bitaxeorg/bitaxeBonanza/3d/BZM2.step

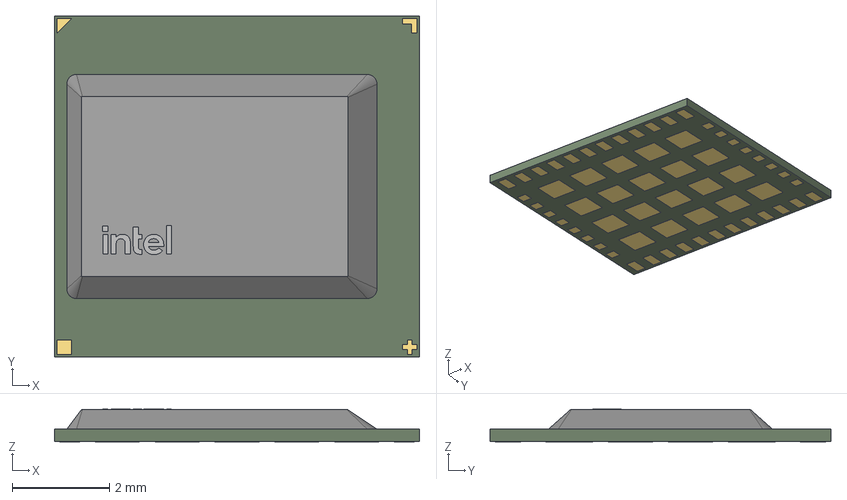
[picture p16: CAD file, 2026-02-11]
3d/BZM2.step
7.50 x 7.00 x 0.669 mm
substrate_part
die_part
underfill_part
intelLogo_part
pin1_part
square_part
plus_part
bracket_part
pads_part
