bitaxeorg/bitaxeBonanza/3d/IND_-1R5MC_SUM.step

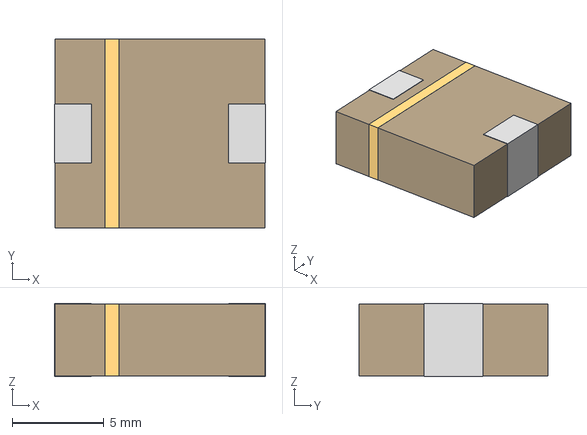
[picture p17: CAD file, 2026-02-11]
3d/IND_-1R5MC_SUM.step
11.5 x 10.3 x 3.99 mm
