bitaxeorg/bitaxeBonanza/3d/Coilcraft-XAL1060.STEP

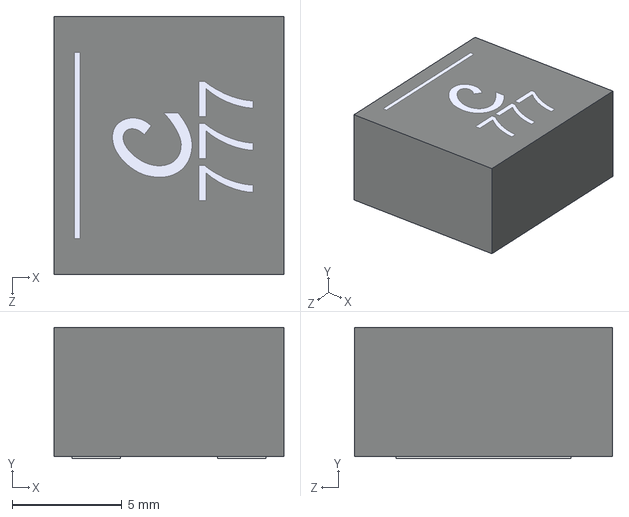
[picture p18: CAD file, 2026-02-11]
3d/Coilcraft-XAL1060.STEP
10.5 x 6.00 x 11.8 mm
