bitaxeorg/bitaxeBonanza/3d/TSM-104-01-L-SH-A.stp

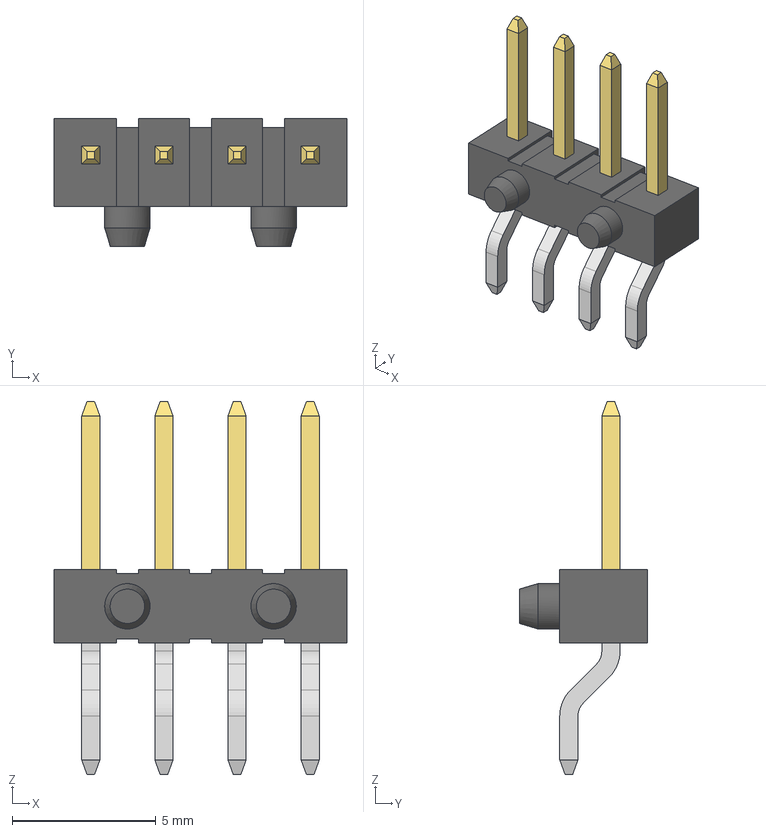
[picture p19: CAD file, 2026-02-11]
3d/TSM-104-01-L-SH-A.stp
10.2 x 4.44 x 13.0 mm
TSM-104-01-SH-A_body
T-1S6-08-L(-01-4-SH)
T-1S6-08-L(-01-4-SH)2
