bitaxeorg/bitaxeBonanza/3d/DCK0006A.stp

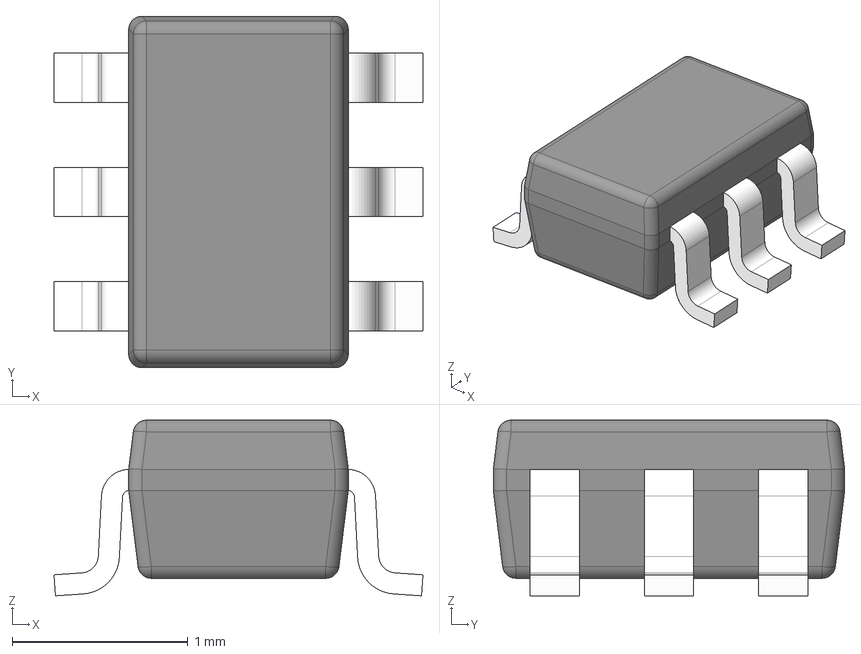
[picture p20: CAD file, 2026-02-11]
3d/DCK0006A.stp
2.10 x 2.00 x 1.00 mm
BODY-SOT
LEAD-SOT x 6
PIN1-ID
