bitaxeorg/bitaxeBonanza/3d/Fan 60x60x25mm.stp

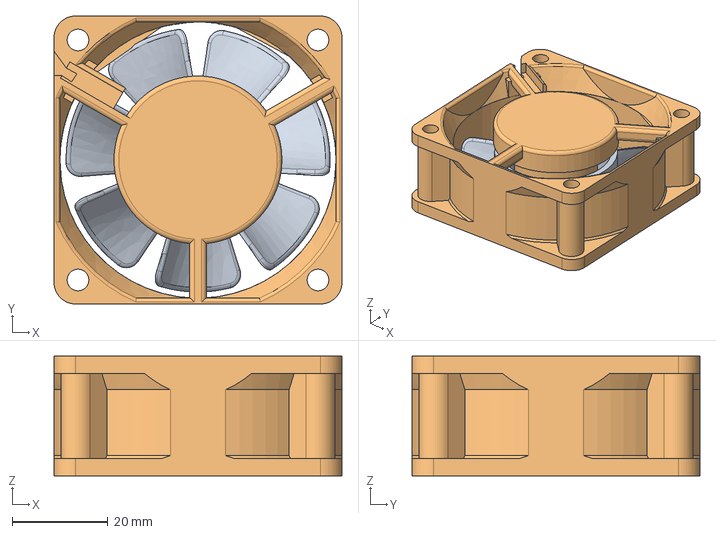
[picture p21: CAD file, 2026-02-11]
3d/Fan 60x60x25mm.stp
60.0 x 60.0 x 25.0 mm
