bitaxeorg/bitaxeBonanza/3d/RaspberryPi_Pico_W.step

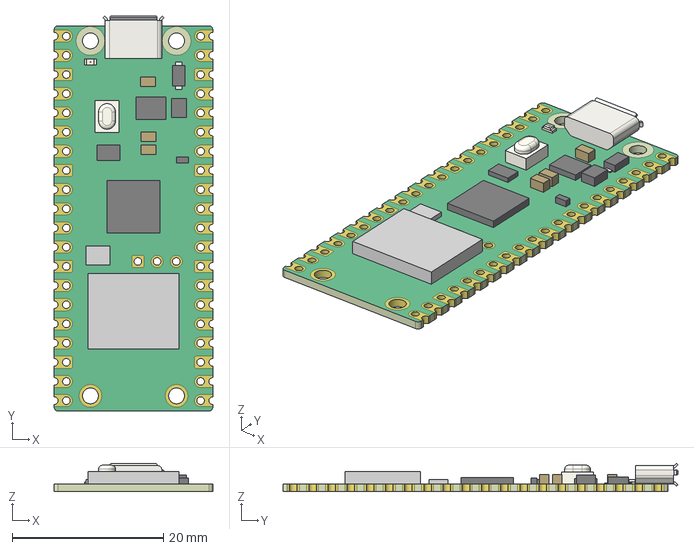
[picture p22: CAD file, 2026-02-11]
3d/RaspberryPi_Pico_W.step
21.0 x 52.3 x 3.75 mm
