bitaxeorg/bitaxeBonanza/3d/GT heatsink.step

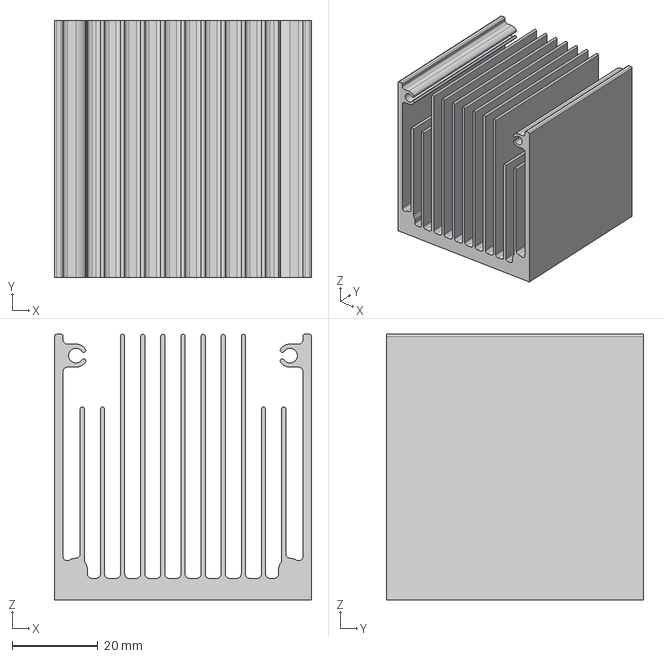
[picture p23: CAD file, 2025-06-24]
3d/GT heatsink.step
60.0 x 60.0 x 62.0 mm
