bitaxeorg/bitaxeBonanza/3d/FPC-SMD_P0.50-8P_FGS-XJ-H2.0.step

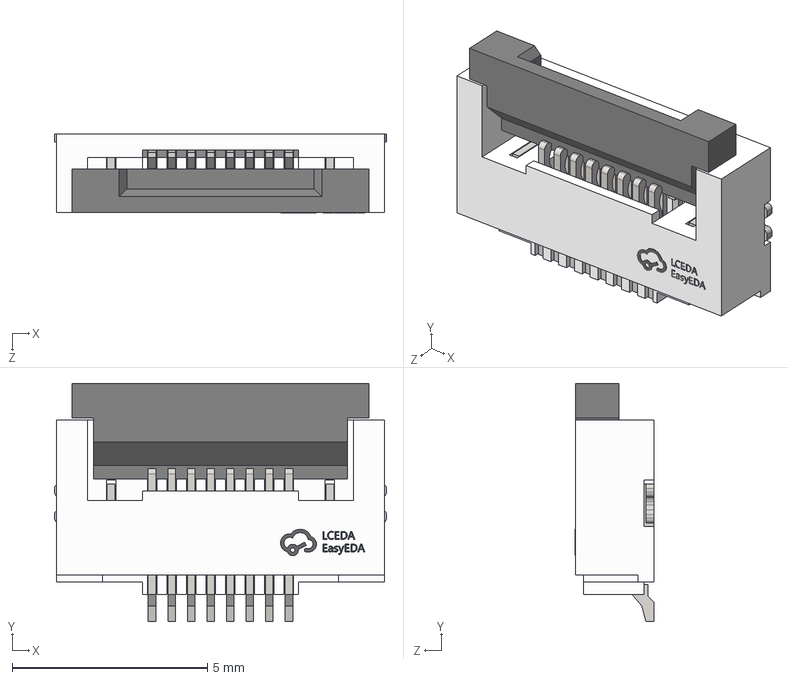
[picture p24: CAD file, 2025-06-20]
3d/FPC-SMD_P0.50-8P_FGS-XJ-H2.0.step
8.50 x 6.10 x 2.01 mm
