bitaxeorg/bitaxeBonanza/3d/FFC2B35-08-T.STEP

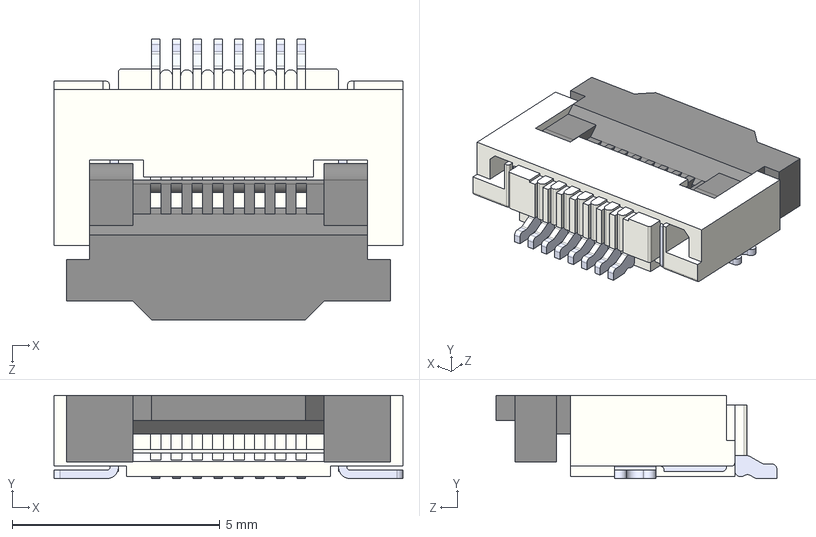
[picture p25: CAD file, 2025-06-20]
3d/FFC2B35-08-T.STEP
8.40 x 2.00 x 6.76 mm
