bitaxeorg/bitaxeBonanza/3d/BZM2model.step

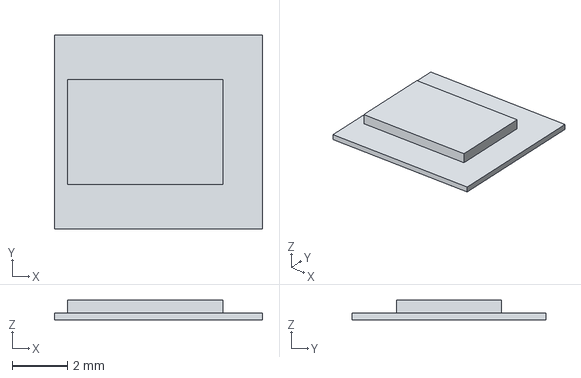
[picture p27: CAD file, 2025-06-20]
3d/BZM2model.step
7.50 x 7.00 x 0.71 mm
