bitaxeorg/bitaxeBonanza/3d/SOD-323FL_UMD2__ROM.step

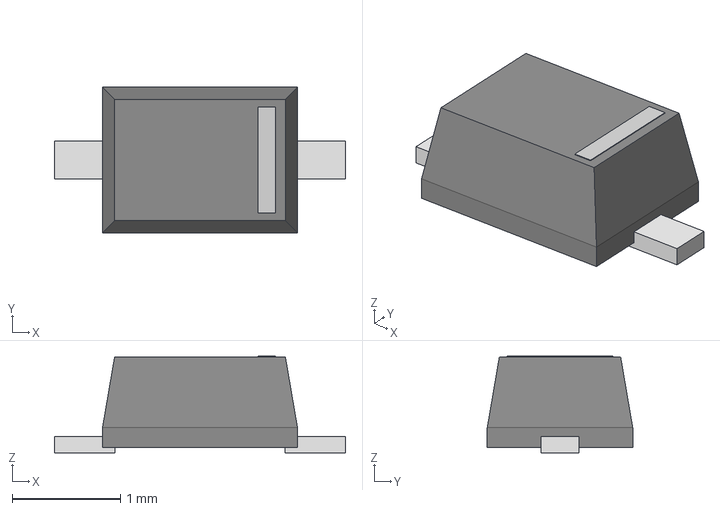
[picture p28: CAD file, 2025-06-12]
3d/SOD-323FL_UMD2__ROM.step
2.69 x 1.35 x 0.895 mm
