bitaxeorg/bitaxeBonanza/3d/DISST7789-176x320.STEP

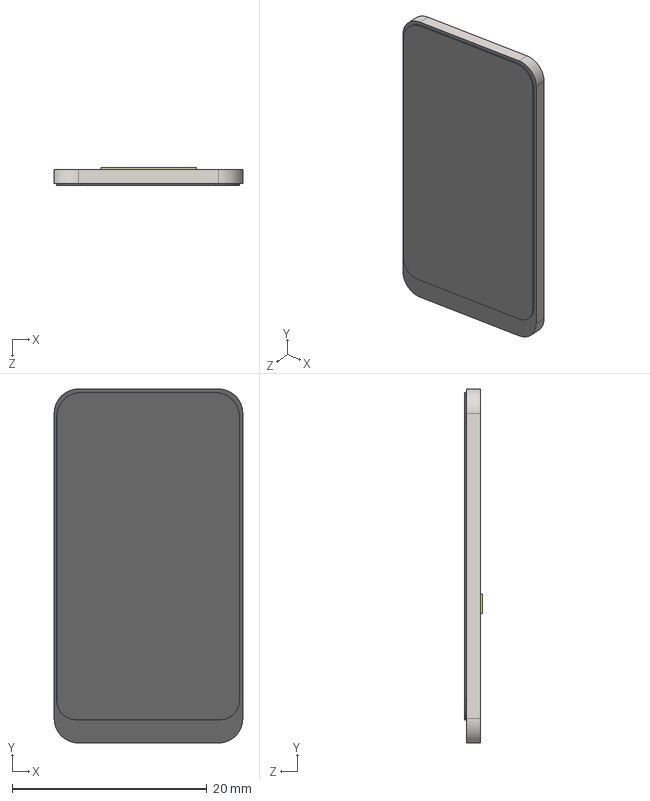
[picture p29: CAD file, 2025-03-25]
3d/DISST7789-176x320.STEP
19.4 x 36.4 x 1.86 mm
