bitaxeorg/bitaxeBonanza/3d/TXB0104RGYR.STEP

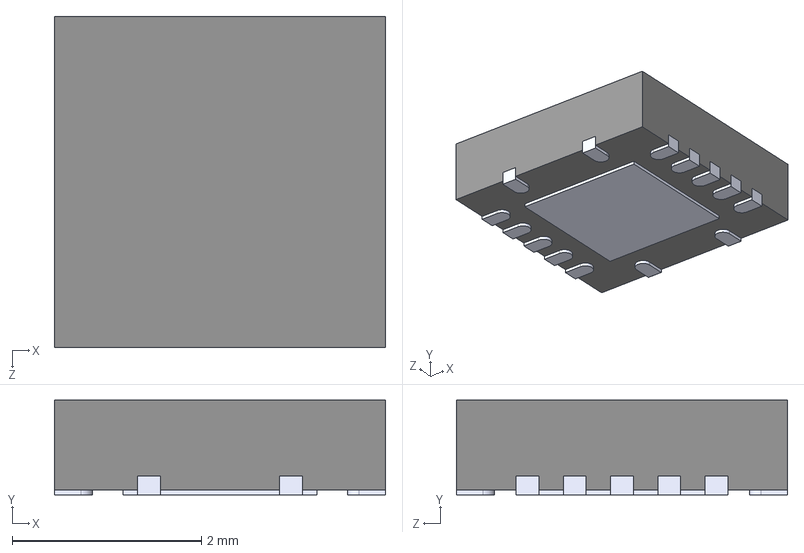
[picture p30: CAD file, 2025-03-25]
3d/TXB0104RGYR.STEP
3.50 x 1.00 x 3.50 mm
