bitaxeorg/bitaxeBonanza/3d/ESP32-S3-WROOM-1-N8R2--3DModel-STEP-56544.STEP

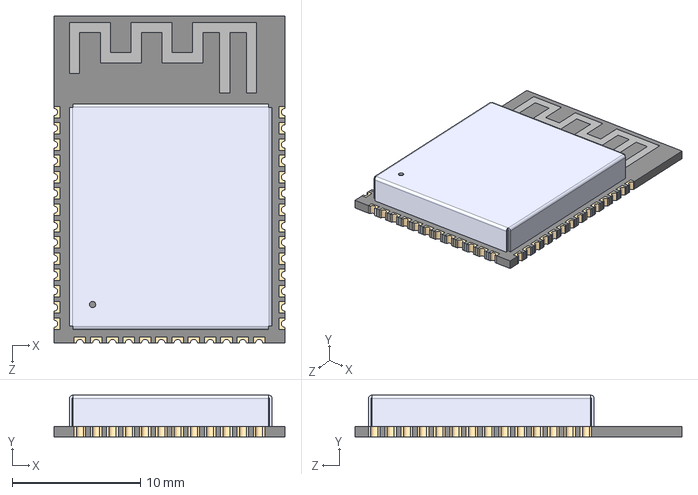
[picture p31: CAD file, 2025-03-25]
3d/ESP32-S3-WROOM-1-N8R2--3DModel-STEP-56544.STEP
18.0 x 3.25 x 25.5 mm
