bitaxeorg/bitaxeBonanza/3d/TPS546D24ARVFR.step

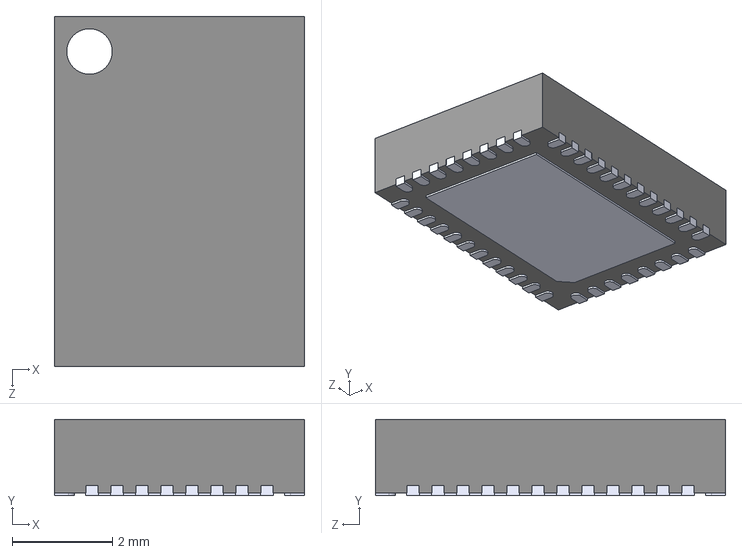
[picture p32: CAD file, 2025-03-25]
3d/TPS546D24ARVFR.step
5.00 x 1.52 x 7.00 mm
