bitaxeorg/bitaxeBonanza/3d/BitaxeGT_heatsink.step

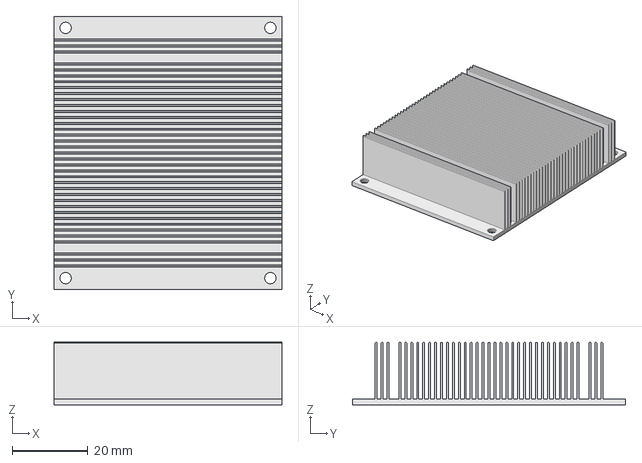
[picture p33: CAD file, 2025-03-25]
3d/BitaxeGT_heatsink.step
60.0 x 72.0 x 16.5 mm
