bitaxeorg/bitaxeBonanza/3d/BM04B-SRSS-TB.STEP

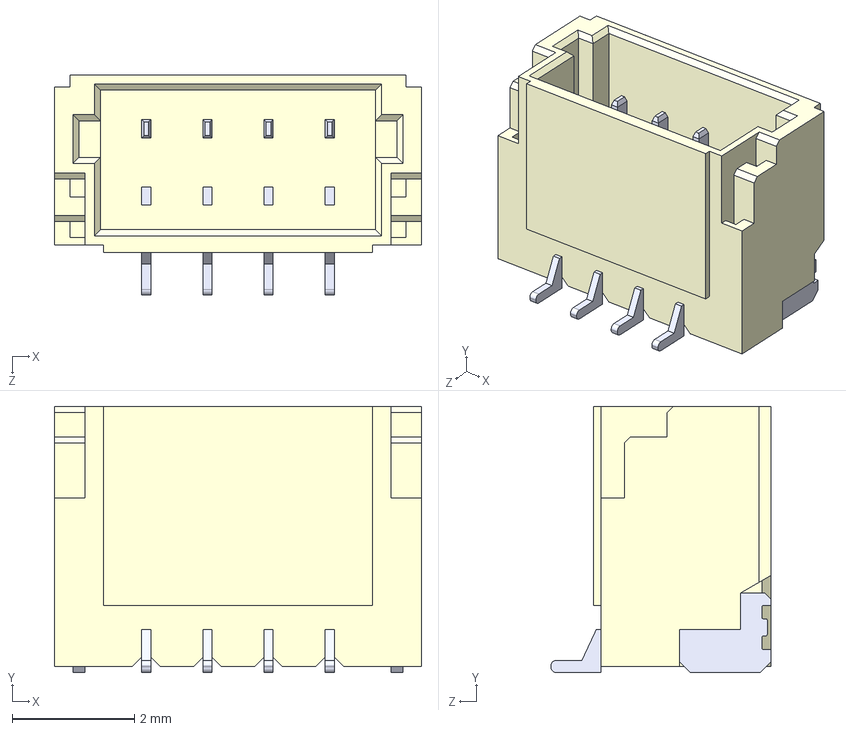
[picture p34: CAD file, 2025-03-25]
3d/BM04B-SRSS-TB.STEP
6.00 x 4.35 x 3.60 mm
