bitaxeorg/bitaxeBonanza/3d/BM1368xx.stp

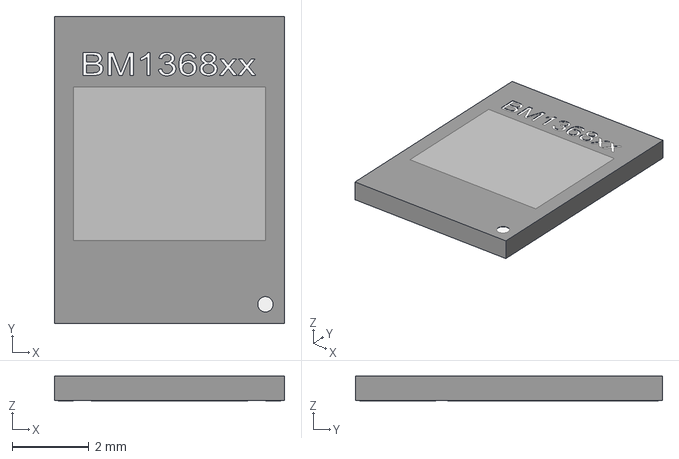
[picture p35: CAD file, 2025-03-25]
3d/BM1368xx.stp
6.00 x 8.00 x 0.65 mm
