bitaxeorg/bitaxeBonanza/3d/CUI_DEVICES_PJ-036AH-SMT-TR.step

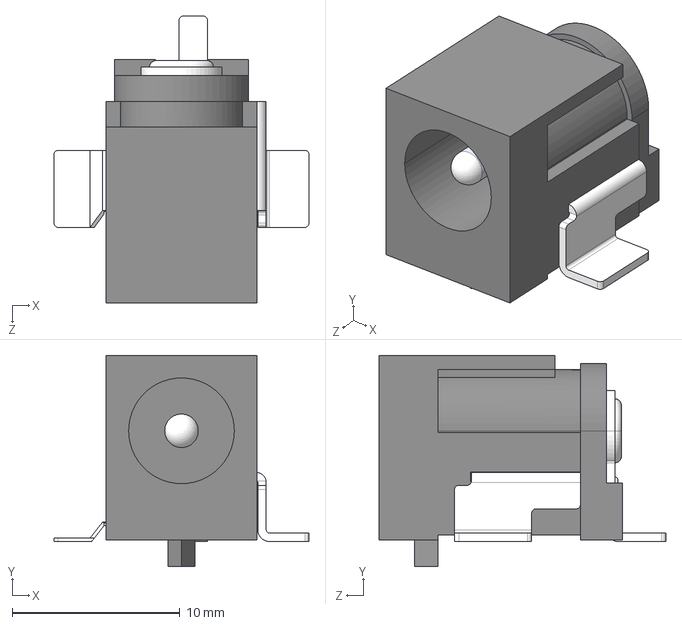
[picture p36: CAD file, 2025-03-25]
3d/CUI_DEVICES_PJ-036AH-SMT-TR.step
15.2 x 12.6 x 17.1 mm
