bitaxeorg/bitaxeBonanza/3d/SLC1175-271MEC_COC.step

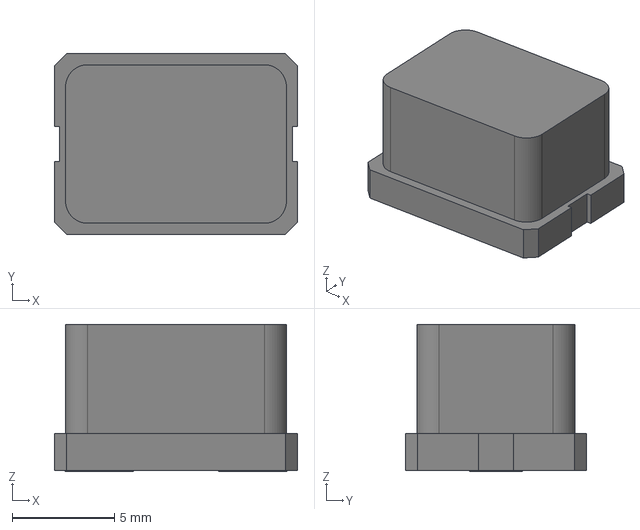
[picture p37: CAD file, 2025-03-25]
3d/SLC1175-271MEC_COC.step
11.9 x 8.83 x 7.19 mm
