bitaxeorg/bitaxeBonanza/3d/IHLP2020CZ.step

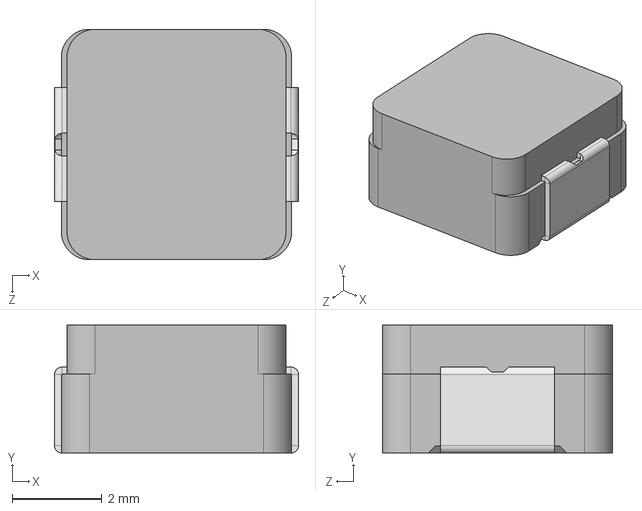
[picture p39: CAD file, 2025-03-25]
3d/IHLP2020CZ.step
5.45 x 2.86 x 5.15 mm
