bitaxeorg/bitaxeBonanza/3d/TSOT-23-5_RIT.step

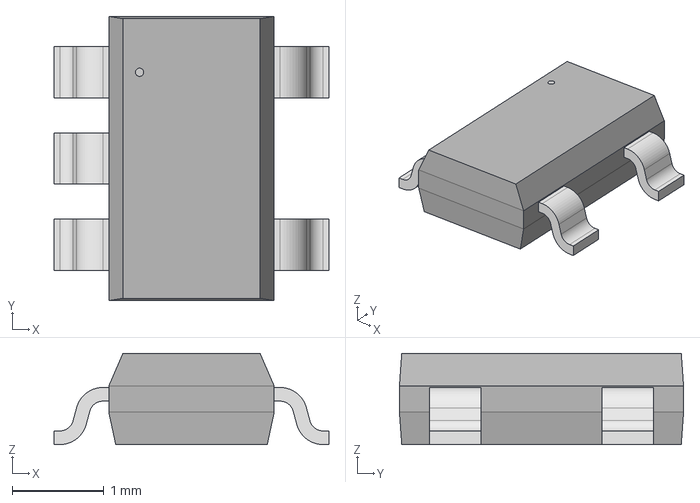
[picture p41: CAD file, 2025-03-25]
3d/TSOT-23-5_RIT.step
3.00 x 3.10 x 0.993 mm
