bitaxeorg/bitaxeBonanza/3d/DRC0010J.stp

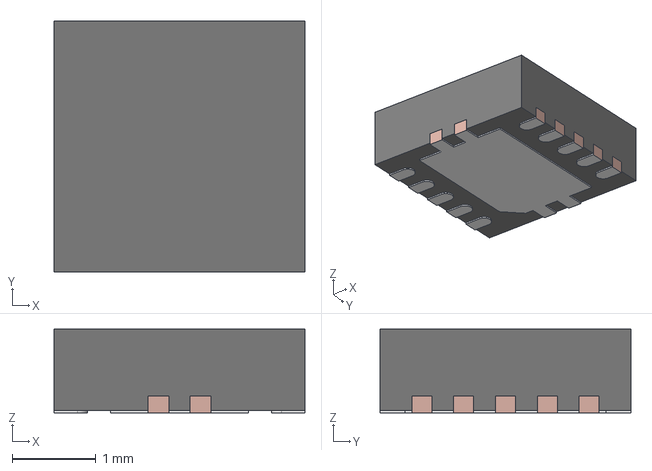
[picture p42: CAD file, 2025-03-25]
3d/DRC0010J.stp
3.00 x 3.00 x 1.00 mm
BODY-SON
FRAME-DRC0010J
