bitaxeorg/bitaxeBonanza/3d/XTAL_SC32S-7PF20PPM_EPS.step

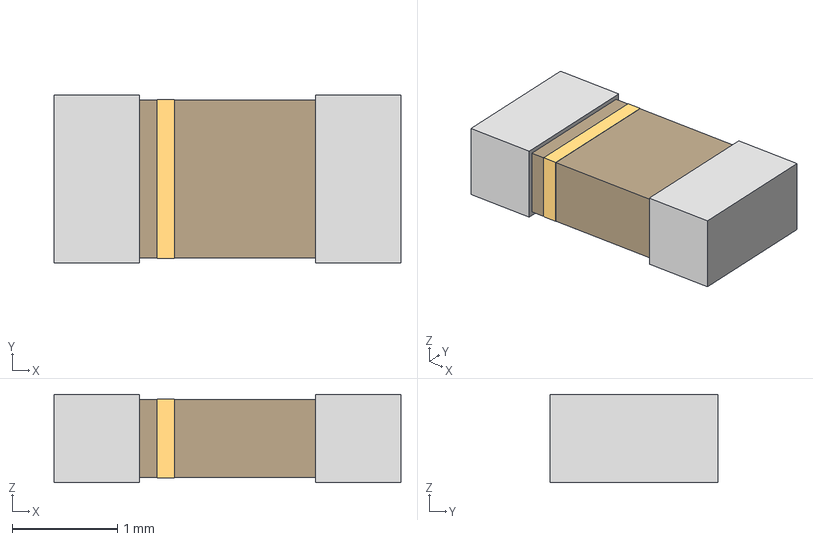
[picture p43: CAD file, 2025-03-25]
3d/XTAL_SC32S-7PF20PPM_EPS.step
3.30 x 1.60 x 0.838 mm
