bitaxeorg/bitaxeBonanza/3d/SOT-23-5_M5_MCH.step

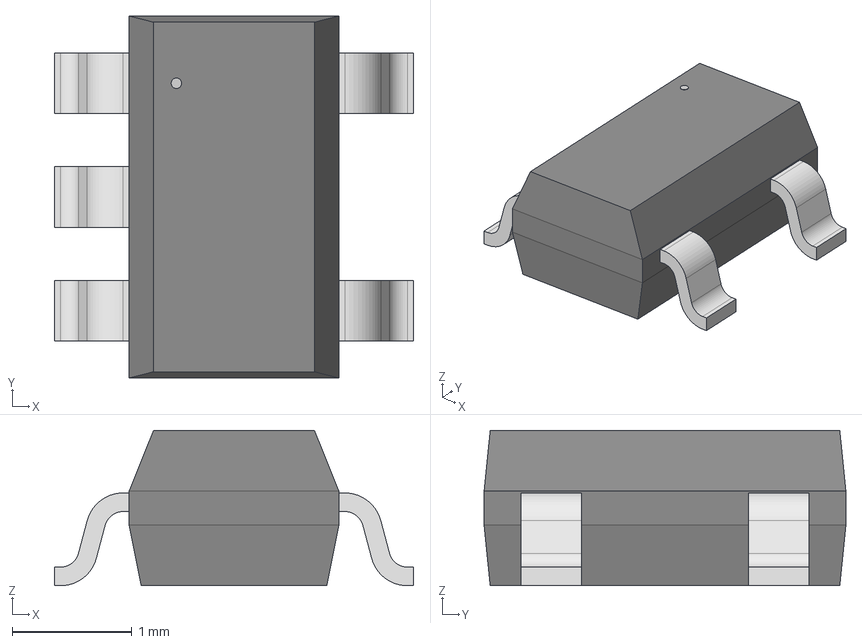
[picture p45: CAD file, 2025-03-25]
3d/SOT-23-5_M5_MCH.step
3.00 x 3.02 x 1.30 mm
