bitaxeorg/bitaxeBonanza/3d/DQH0008A.stp

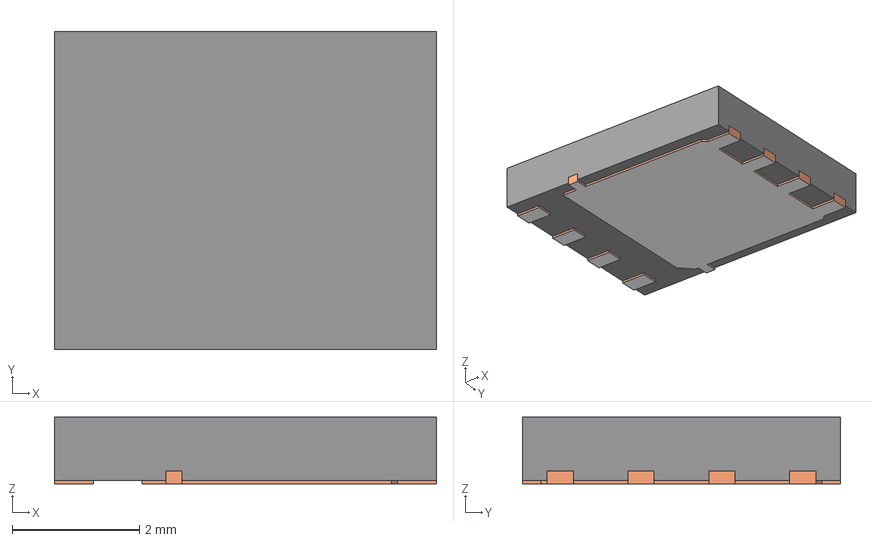
[picture p46: CAD file, 2025-03-25]
3d/DQH0008A.stp
6.00 x 5.00 x 1.05 mm
BODY-SON
FRAME-DQH0008A
PIN1-ID
