bitaxeorg/bitaxeBonanza/3d/Bitaxe_Heatsink.step

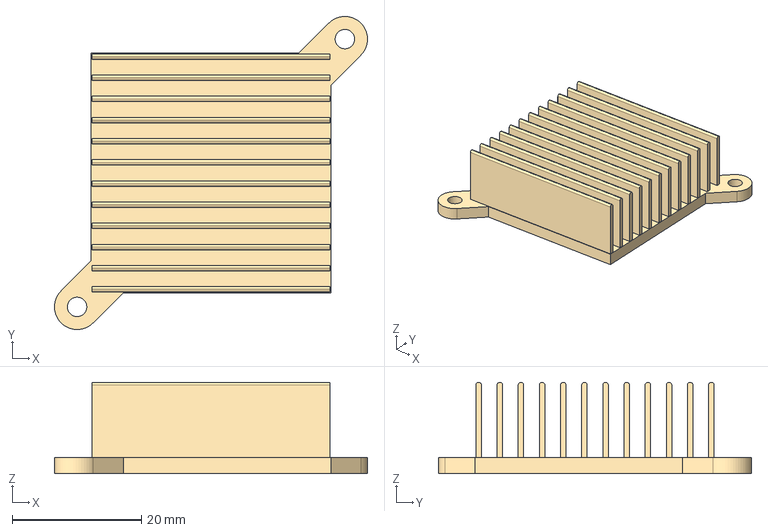
[picture p47: CAD file, 2025-03-25]
3d/Bitaxe_Heatsink.step
48.4 x 48.4 x 14.1 mm
