bitaxeorg/bitaxeBonanza/3d/oscillator3.2x2.5.step

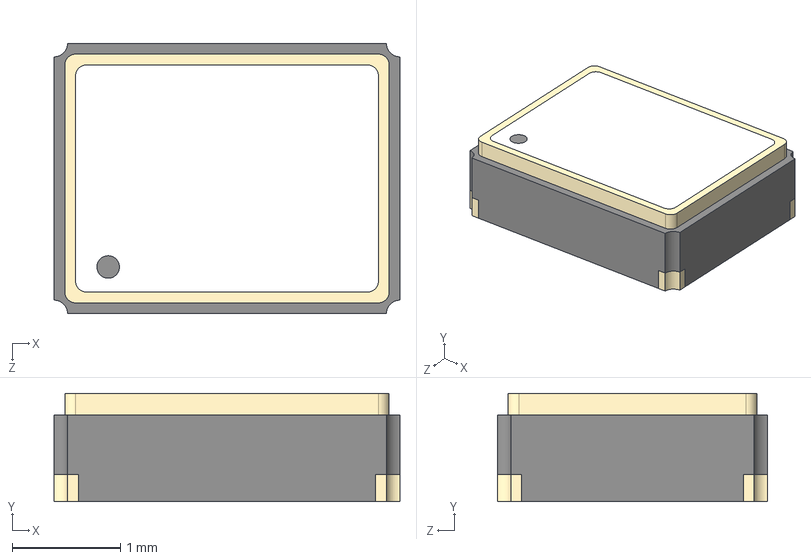
[picture p48: CAD file, 2025-03-25]
3d/oscillator3.2x2.5.step
3.20 x 1.00 x 2.50 mm
