bitaxeorg/bitaxeBonanza/3d/c-63862-1-r-3d.stp

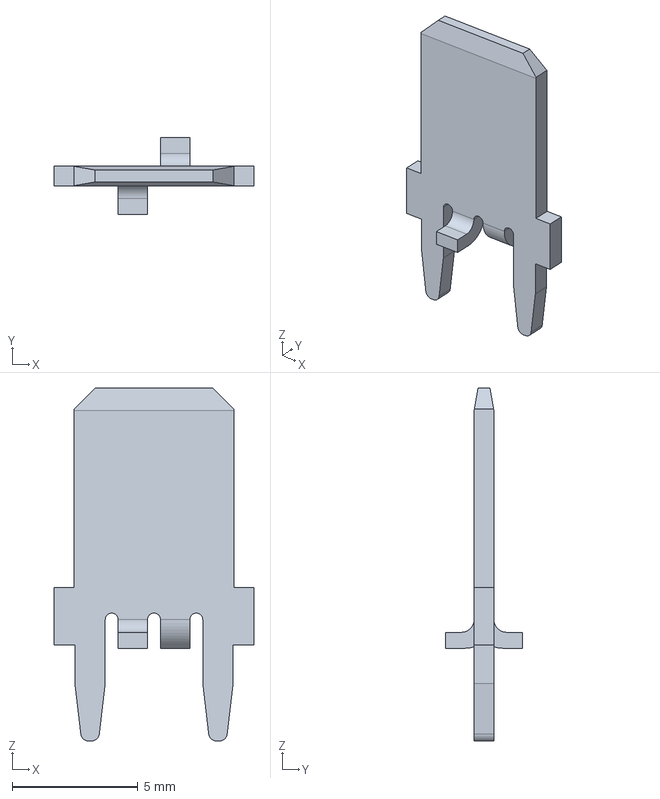
[picture p49: CAD file, 2025-03-25]
3d/c-63862-1-r-3d.stp
7.92 x 3.07 x 14.0 mm
