bitaxeorg/bitaxeBonanza/3d/Cree_PLCC6.stp

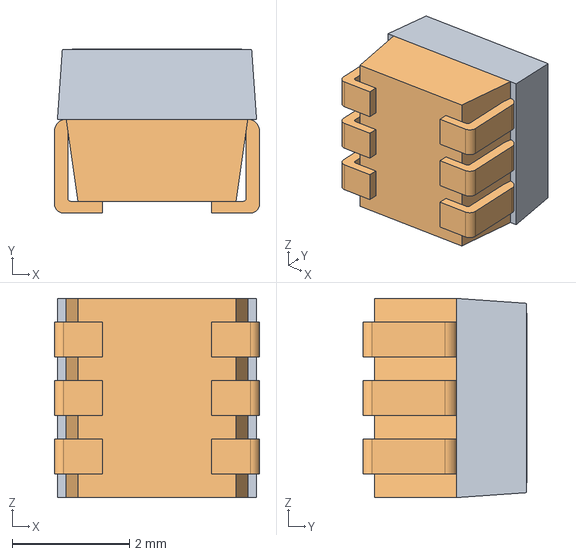
[picture p54: CAD file, 2025-03-25]
3d/Cree_PLCC6.stp
3.50 x 2.80 x 3.40 mm
CORPS-DPLACER_COPI0001_1
CORPS-DPLACER_COPI0002_1
