bitaxeorg/bitaxeBonanza/3d/CUI_DEVICES_PJ-002AH.step

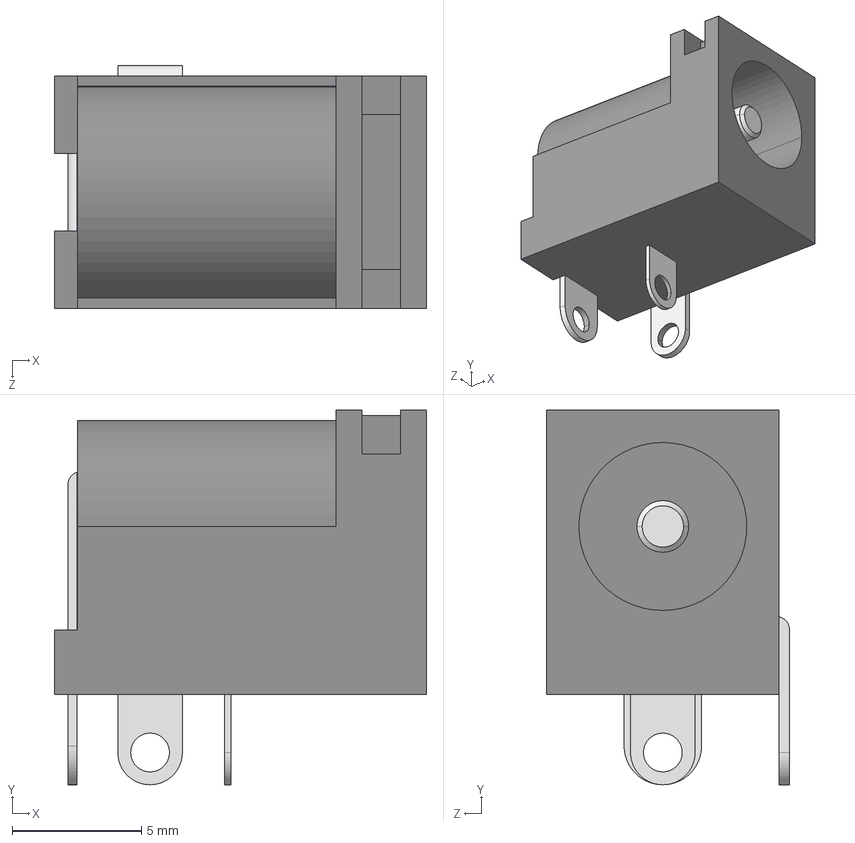
[picture p58: CAD file, 2025-03-25]
3d/CUI_DEVICES_PJ-002AH.step
14.4 x 14.5 x 9.40 mm
