bitaxeorg/bitaxeBonanza/3d/CUI_DEVICES_PJ-037AH.step

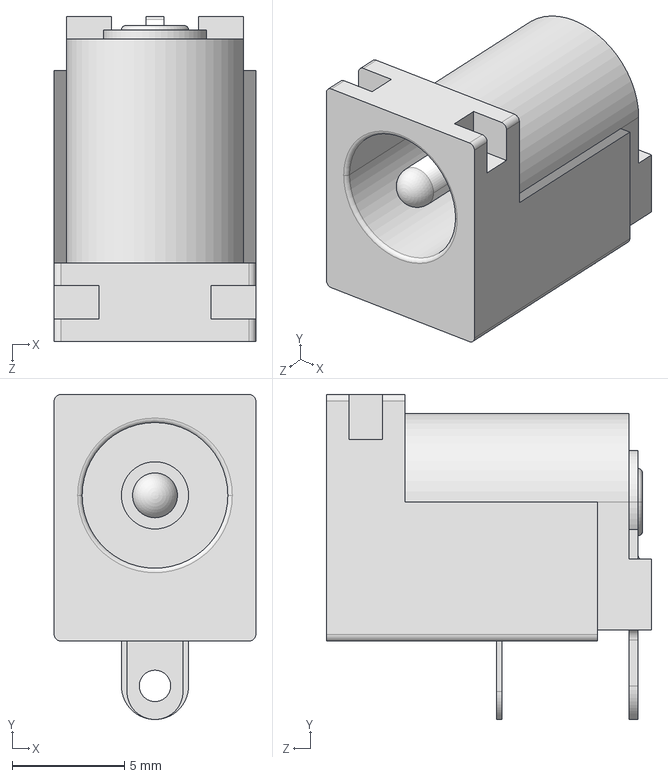
[picture p59: CAD file, 2025-03-25]
3d/CUI_DEVICES_PJ-037AH.step
9.00 x 14.5 x 14.5 mm
