bitaxeorg/bitaxeBonanza/3d/DQG0008A.stp

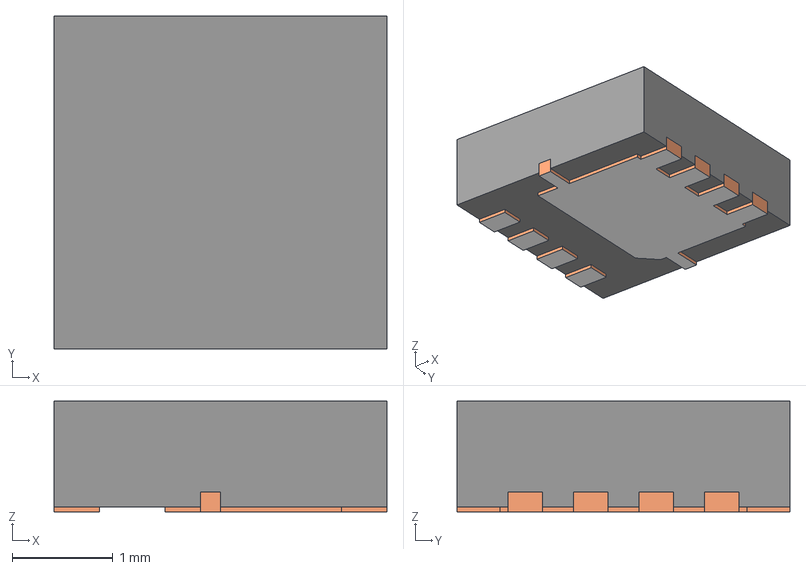
[picture p60: CAD file, 2025-03-25]
3d/DQG0008A.stp
3.30 x 3.30 x 1.10 mm
BODY-SON
FRAME-DQG0008A
PIN1-ID
