bitaxeorg/bitaxeBonanza/3d/SMV_z90.stp

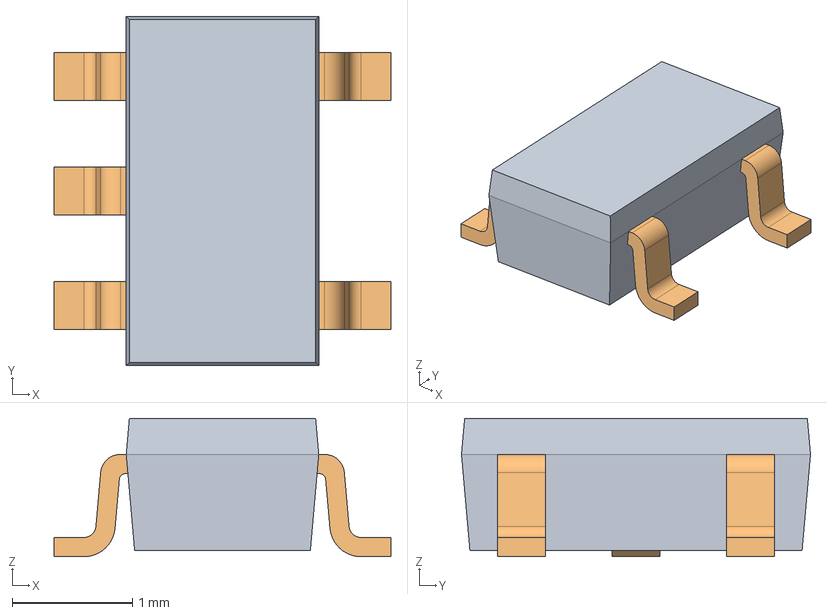
[picture p61: CAD file, 2025-03-25]
3d/SMV_z90.stp
2.80 x 2.90 x 1.15 mm
