bitaxeorg/bitaxeBonanza/3d/XRCGB27M120F3M10R0_MUR.step

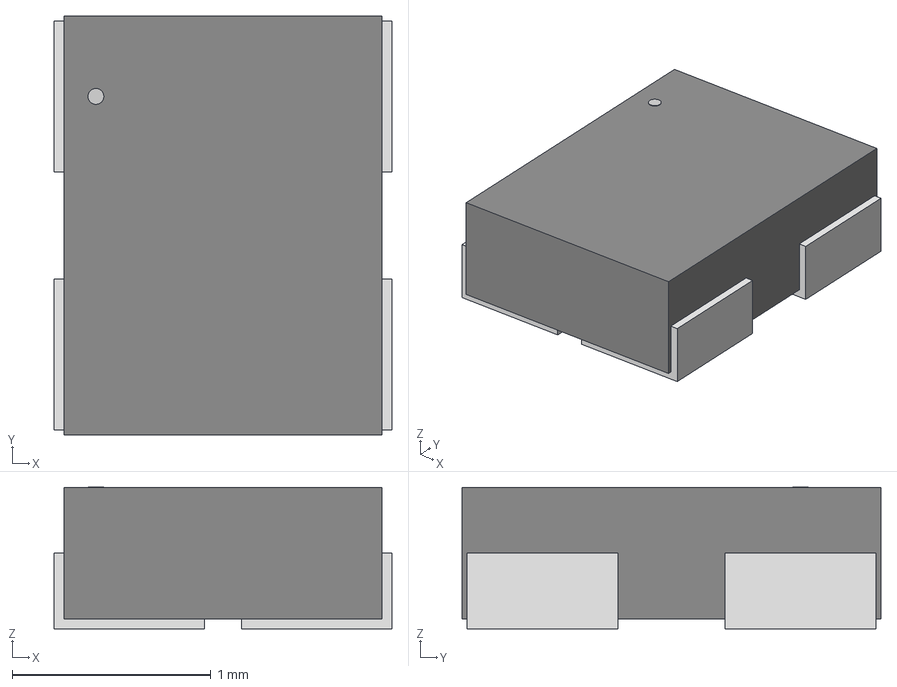
[picture p62: CAD file, 2025-03-25]
3d/XRCGB27M120F3M10R0_MUR.step
1.70 x 2.11 x 0.714 mm
