bitaxeorg/bitaxeBonanza/3d/DQN0004A.stp

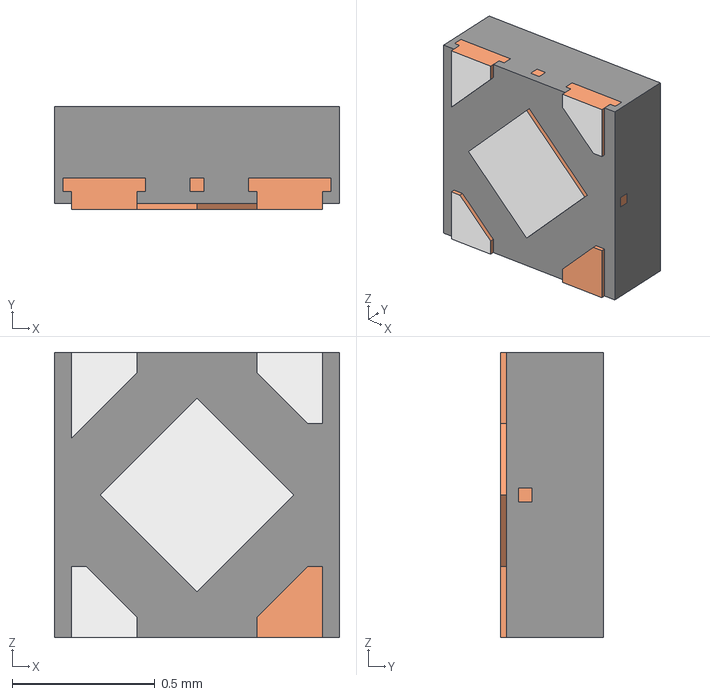
[picture p64: CAD file, 2025-03-25]
3d/DQN0004A.stp
1.00 x 0.36 x 1.00 mm
MOLD-SNB04A
FRAME-SNB04A
