bitaxeorg/bitaxeBonanza/3d/XT30PW-M.stp

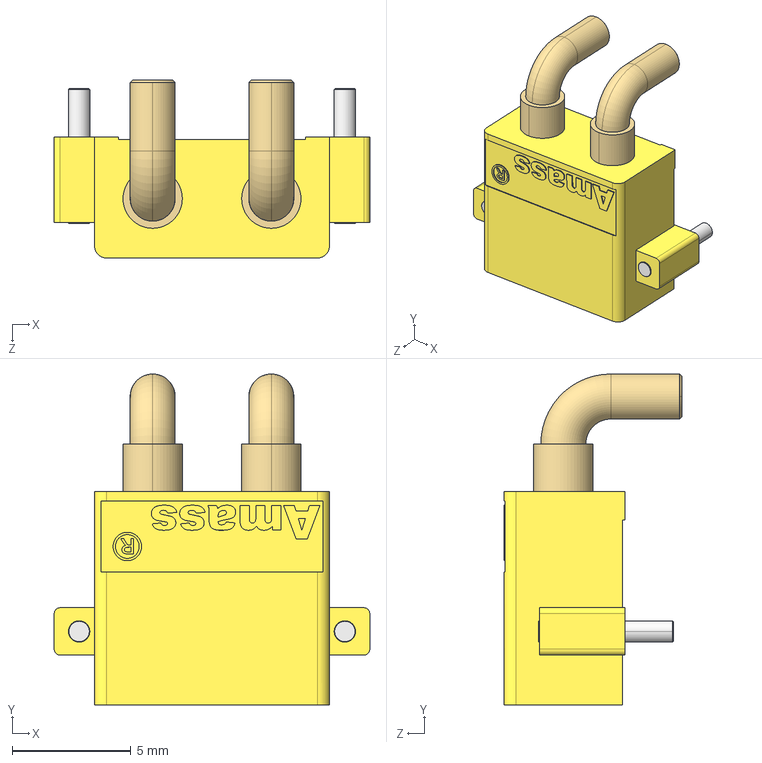
[picture p65: CAD file, 2025-03-25]
3d/XT30PW-M.stp
13.3 x 13.9 x 7.50 mm
