bitaxeorg/bitaxeBonanza/3d/bm1370.step

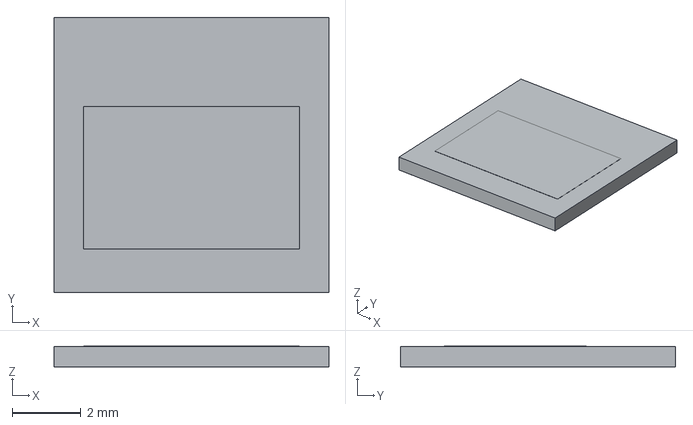
[picture p66: CAD file, 2025-03-25]
3d/bm1370.step
8.00 x 8.00 x 0.61 mm
