bitaxeorg/bitaxeBonanza/3d/DRL0006A.stp

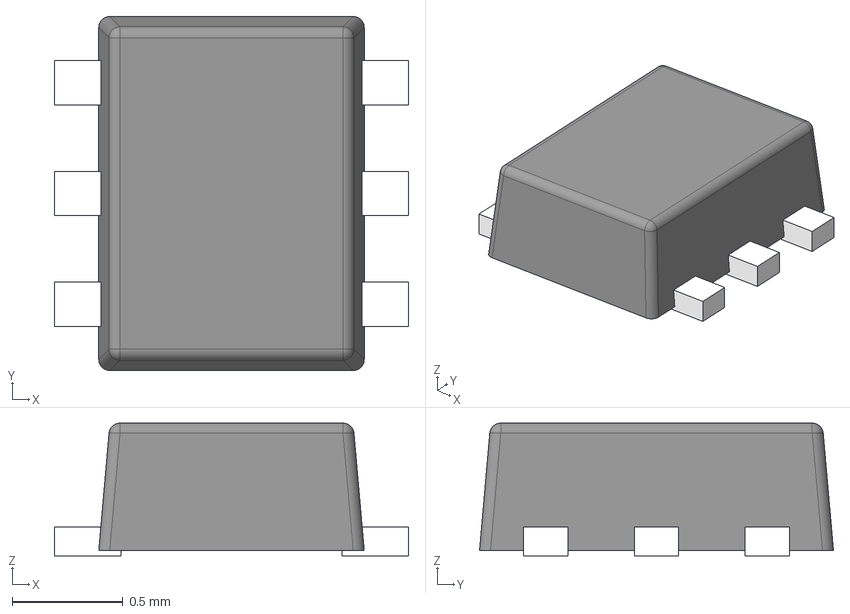
[picture p67: CAD file, 2025-03-25]
3d/DRL0006A.stp
1.60 x 1.60 x 0.6 mm
FRAME-DRL0006A
BODY-SOT
PIN1-ID
