bitaxeorg/bitaxeBonanza/3d/QFN16_4X4_MCH.step

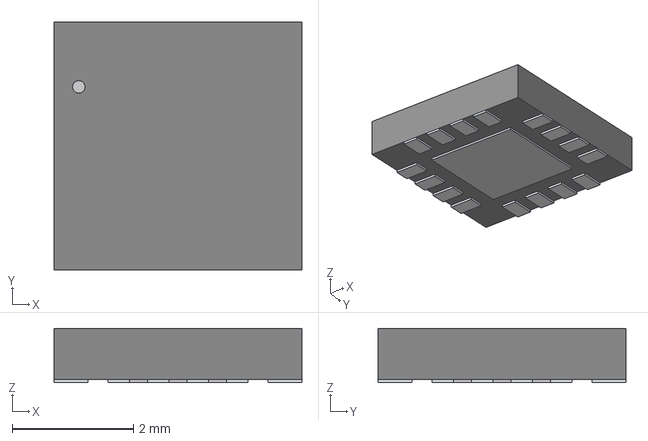
[picture p68: CAD file, 2025-03-25]
3d/QFN16_4X4_MCH.step
4.09 x 4.09 x 0.892 mm
