bitaxeorg/bitaxeBonanza/3d/Coilcraft-SLC1175.STEP

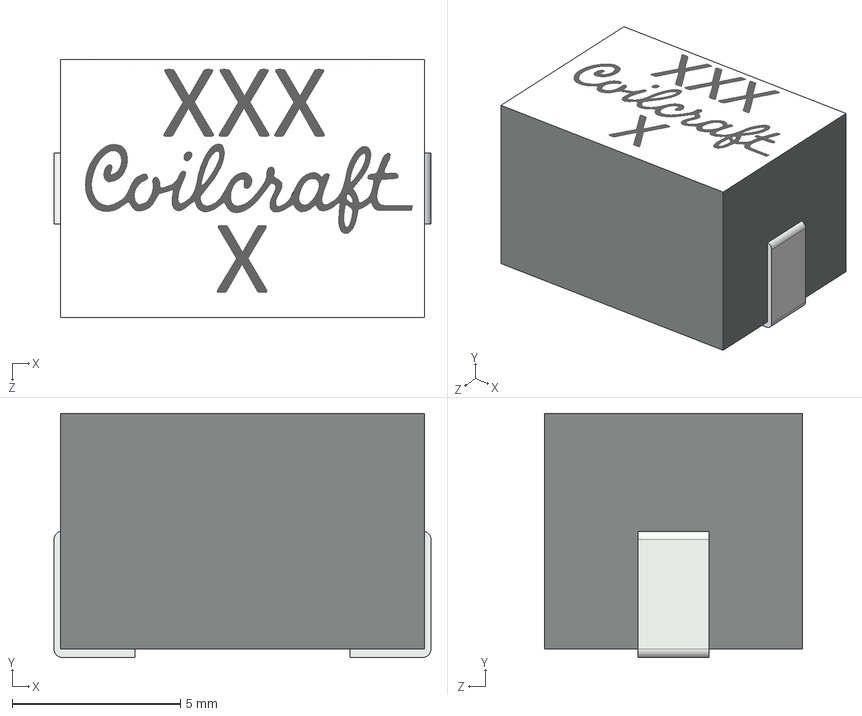
[picture p71: CAD file, 2025-03-25]
3d/Coilcraft-SLC1175.STEP
11.2 x 7.25 x 7.65 mm
