bitaxeorg/bitaxeBonanza/3d/CS1213AG-tr.stp

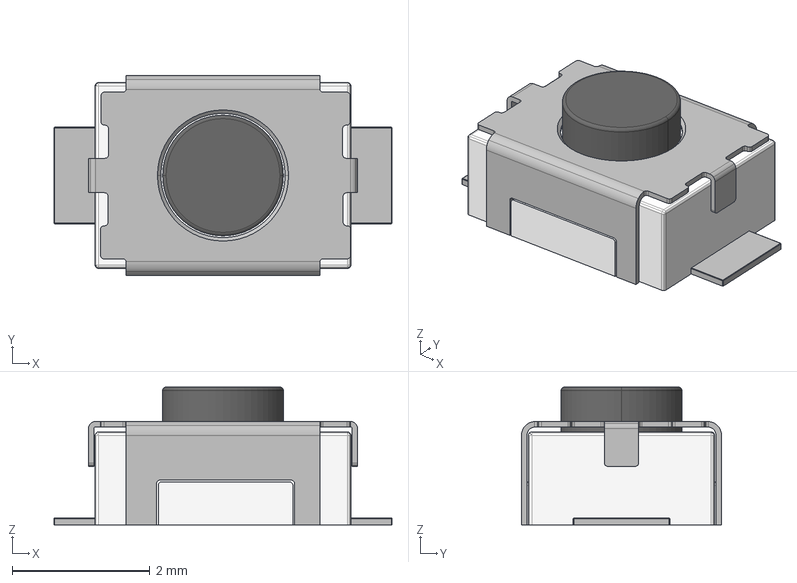
[picture p72: CAD file, 2023-12-13]
3d/CS1213AG-tr.stp
4.90 x 2.90 x 2.00 mm
