bitaxeorg/bitaxeBonanza/3d/ECS-3225MV-500-CN-TR.STEP

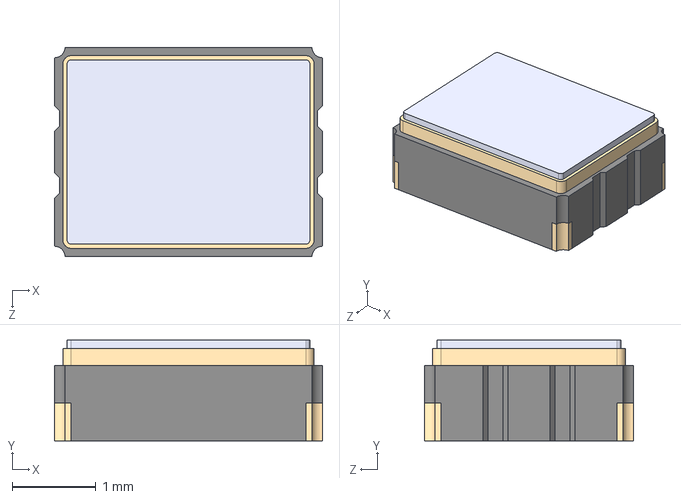
[picture p73: CAD file, 2023-12-02]
3d/ECS-3225MV-500-CN-TR.STEP
3.20 x 1.20 x 2.50 mm
