bitaxeorg/bitaxeBonanza/WebBench/WBDesign-1004x.pdf

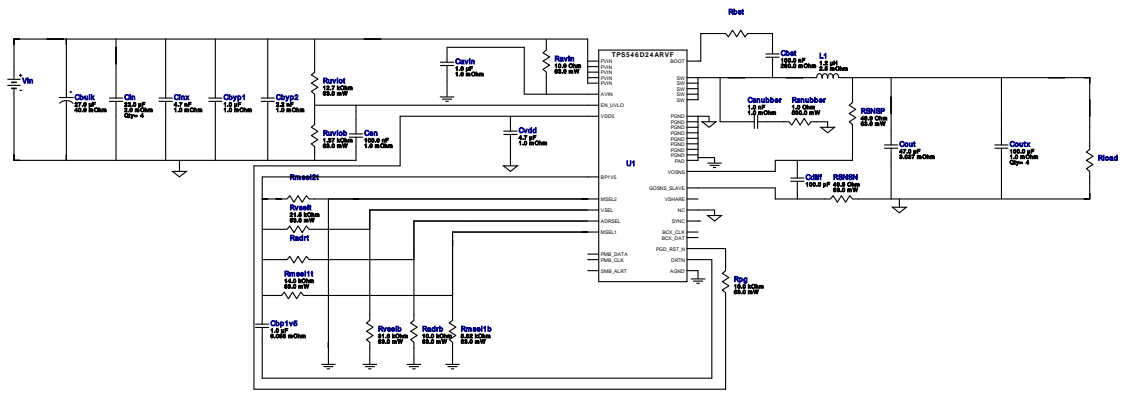
[picture p74: figure]
Cbyp2 2.2 nF 1.0 m Ohm; Cen 100.0 nF 1.0 m Ohm; Rsnubber 1.0 Ohm; Ruvlob 1.37 kOhm 63.0 m W; Cdiff 100.0 pF; Cavin 1.0 µF 1.0 m Ohm Ruvlot 12.7 kOhm; Coutx 100.0 µF 1.0 m Ohm Qty= 4; Cin 22.0 µF 2.0 m Ohm Qty= 4; RSNSN 49.9 Ohm 63.0 m W; Cout 47.0 µF; 3.037 m Ohm; RSNSP 49.9 Ohm 63.0 m W; Cinx 4.7 nF 1.0 m Ohm; Cbp1v5 1.0 µF 6.065 m Ohm; Cbyp1 1.0 µF 1.0 m Ohm; Rvselb 31.6 kOhm 63.0 m W; Rbst; Rpg 10.0 kOhm 63.0 m W; Ravin 10.0 Ohm 63.0 m W; Radrt; Rm sel2t; Rvselt 21.5 kOhm; L1 1.2 µH 2.5 m Ohm; Csnubber 1.0 nF; 1.0 m Ohm; Cbulk 27.0 µF 40.0 m Ohm; Cvdd 4.7 µF 1.0 m Ohm; Rm sel1t 14.0 kOhm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

Copyright © 2025, Texas Instruments Incorporated | 1 | ti.com/webench

WEBENCH®
Design Report TPS546D24ARVFR : TPS546D24ARVFR 11V-13V to 2.80V @ 20A October 2, 2025 14:52:55 GMT-05:00

## WEBENCH ® Design Report

Design : 114 TPS546D24ARVFR
TPS546D24ARVFR 11V-13V to 2.80V @ 20A

VinMin = 11.0V
VinMax = 13.0V
Vout = 2.8V
Vout Sch = 2.8V
Iout = 20.0A

Device = TPS546D24ARVFR
Topology = Buck
Created = 2025-09-15 13:40:46.376 BOM Cost = $8.70
BOM Count = 34
Total Pd = 3.45W
1. Do not place Rmsel2t, Radrt resistors. Place 0 Ohm resistor for Rbst.

### Design Alerts

Component Selection Information
DESIGN ERROR MESSAGE: For the entered input condition Phase margin is 44 ( less than 45 degree), try changing the compensation gains to match the recommended VLOOP and ILOOP in the OPERATING VALUES Compensation tab. Try to increase switching frequency or reduce inductance. The TPS546D24A is a PMBus(TM) device with key features listed below: PMBus(TM) features marked with * are included in WEBENCH(R) Power Designer. - Adaptive Voltage Scaling (AVS) through VOUT_COMMAND*, - Output voltage and current monitoring,
- Thermal Shutdown, - Programmable over current protection, - OCP,OV, UV, OT Levels, - Selectable Internal Compensation*, - Selectable Switching Frequency*, - Turn-On and Turn-Off Delays, - UVLO*, Soft-Start*,OCP* and Soft-Stop. Use the Advanced Options on the left side to set the PMBus(TM) commands. Please refer to the TPS546D24A datasheet and visit http://www.ti.com/pmbus for more information.

## Electrical BOM

Name | Manufacturer | Part Number | Properties | Qty Price | Footprint
Cavin | Taiyo Yuden | TMK212BJ105KG-T Series= X5R | Cap= 1.0 uF ESR= 1.0 mOhm VDC= 25.0 V IRMS= 0.0 A
1 | $0.03
| | | | | 0805 7 mm²
Cbp1v5 | MuRata | GRM188R60J105KA01D (http://psearch.en.murata.com/capacitor/result/smd/?status%3Dall%26pid%3DGRM188R60J105KA01D) Series= X5R

Cap= 1.0 uF
ESR= 6.065 mOhm
VDC= 6.3 V
IRMS= 1.36934 A

1 $0.01
0603 5 mm²
Cbst | AVX | 08053C104KAT2A (http://datasheets.avx.com/X7RDielectric.pdf) Series= X7R

Cap= 100.0 nF
ESR= 280.0 mOhm
VDC= 25.0 V
IRMS= 0.0 A

1 $0.01
0805 7 mm²

Design

Copyright © 2025, Texas Instruments Incorporated | 2 | ti.com/webench
Name | Manufacturer | Part Number | Properties | Qty Price | Footprint
Cbulk | Panasonic | 25SVPF27MX Series= SVPF | Cap= 27.0 uF ESR= 40.0 mOhm VDC= 25.0 V IRMS= 2.45 A
1 | $0.47
| | | | | CAPSMT_62_E61 53 mm²
Cbyp1 | Taiyo Yuden | TMK212BJ105KG-T Series= X5R | Cap= 1.0 uF ESR= 1.0 mOhm VDC= 25.0 V IRMS= 0.0 A
1 | $0.03
| | | | | 0805 7 mm²
Cbyp2 | MuRata | GRM155R61E222KA01D (http://search.murata.co.jp/Ceramy/PnsearchViewAction.do) Series= X5R

Cap= 2.2 nF
ESR= 1.0 mOhm
VDC= 25.0 V
IRMS= 0.0 A

1 $0.01
0402 3 mm²
Cdiff | Kemet | C0201C101K3GACTU (http://www.kemet.com/docfinder?Partnumber%3DC0201C101K3GACTU) Series= C0G/NP0

Cap= 100.0 pF
VDC= 10.0 V
IRMS= 0.0 A

1 $0.01
0201 2 mm²
Cen | MuRata | GRM155R71A104KA01D (http://search.murata.co.jp/Ceramy/PnsearchViewAction.do) Series= X7R

Cap= 100.0 nF
ESR= 1.0 mOhm
VDC= 10.0 V
IRMS= 0.0 A

1 $0.01
0402 3 mm²
Cin | MuRata | GRM32ER61E226KE15L (http://search.murata.co.jp/Ceramy/image/img/A01X/G101/ENG/GRM32ER61E226KE15%2D01.pdf) Series= X5R

Cap= 22.0 uF
ESR= 2.0 mOhm
VDC= 25.0 V
IRMS= 3.67 A

4 $0.23
1210 15 mm²
Cinx | MuRata | GRM155R71E472KA01D (http://search.murata.co.jp/Ceramy/PnsearchViewAction.do) Series= X7R

Cap= 4.7 nF
ESR= 1.0 mOhm
VDC= 25.0 V
IRMS= 0.0 A

1 $0.01
0402 3 mm²
Cout | MuRata | GRM32ER61C476KE15L (http://psearch.en.murata.com/capacitor/result/smd/?status%3Dall%26pid%3DGRM32ER61C476KE15L) Series= X5R

Cap= 47.0 uF
ESR= 3.037 mOhm
VDC= 16.0 V
IRMS= 4.59346 A

1 $0.17
1210_280 15 mm²
Coutx | MuRata | GRM32EC80J107ME20L Series= X6S

Cap= 100.0 uF
ESR= 1.0 mOhm
VDC= 6.3 V
IRMS= 6.0 A

4 $0.17
1210_270 15 mm²
Csnubber Yageo | CC0805KRX7R9BB102 (http://www.yageo.com/documents/recent/UPY%2DGPHC%5FX7R%5F6.3V%2Dto%2D50V%5F7.pdf)
| | Series= X7R

Cap= 1.0 nF
ESR= 1.0 mOhm
VDC= 50.0 V
IRMS= 0.0 A

1 $0.01
0805 7 mm²
Cvdd | MuRata | GRM155R61A475MEAAD (http://search.murata.co.jp/Ceramy/image/img/A01X/G101/ENG/GRM155R61A475MEAA%2D01.pdf) Series= X5R

Cap= 4.7 uF
ESR= 1.0 mOhm
VDC= 10.0 V
IRMS= 0.0 A

1 $0.02
0402_065 3 mm²
L1 | Coilcraft | XAL1060-122MEB (http://www.coilcraft.com/pdfs/xal1060.pdf) | L= 1.2 µH 2.5 mOhm
1 | $1.30

XAL1060 160 mm²
RSNSN | Vishay-Dale | CRCW040249R9FKED (http://www.vishay.com/docs/20035/dcrcwe3.pdf) Series= CRCW..e3

Res= 49.9 Ohm
Power= 63.0 mW
Tolerance= 1.0%

1 $0.01
0402 3 mm²
RSNSP | Vishay-Dale | CRCW040249R9FKED (http://www.vishay.com/docs/20035/dcrcwe3.pdf) Series= CRCW..e3

Res= 49.9 Ohm
Power= 63.0 mW
Tolerance= 1.0%

1 $0.01
0402 3 mm²
Radrb | Vishay-Dale | CRCW040210K0FKED (http://www.vishay.com/docs/20035/dcrcwe3.pdf) Series= CRCW..e3

Res= 10.0 kOhm
Power= 63.0 mW
Tolerance= 1.0%

1 $0.01
0402 3 mm²
Ravin | Vishay-Dale | CRCW040210R0FKED (http://www.vishay.com/docs/20035/dcrcwe3.pdf) Series= CRCW..e3

Res= 10.0 Ohm
Power= 63.0 mW
Tolerance= 1.0%

1 $0.01
0402 3 mm²
Rmsel1b Vishay-Dale | CRCW04025K62FKED (http://www.vishay.com/docs/20035/dcrcwe3.pdf)
| | Series= CRCW..e3

Res= 5.62 kOhm
Power= 63.0 mW
Tolerance= 1.0%

1 $0.01
0402 3 mm²

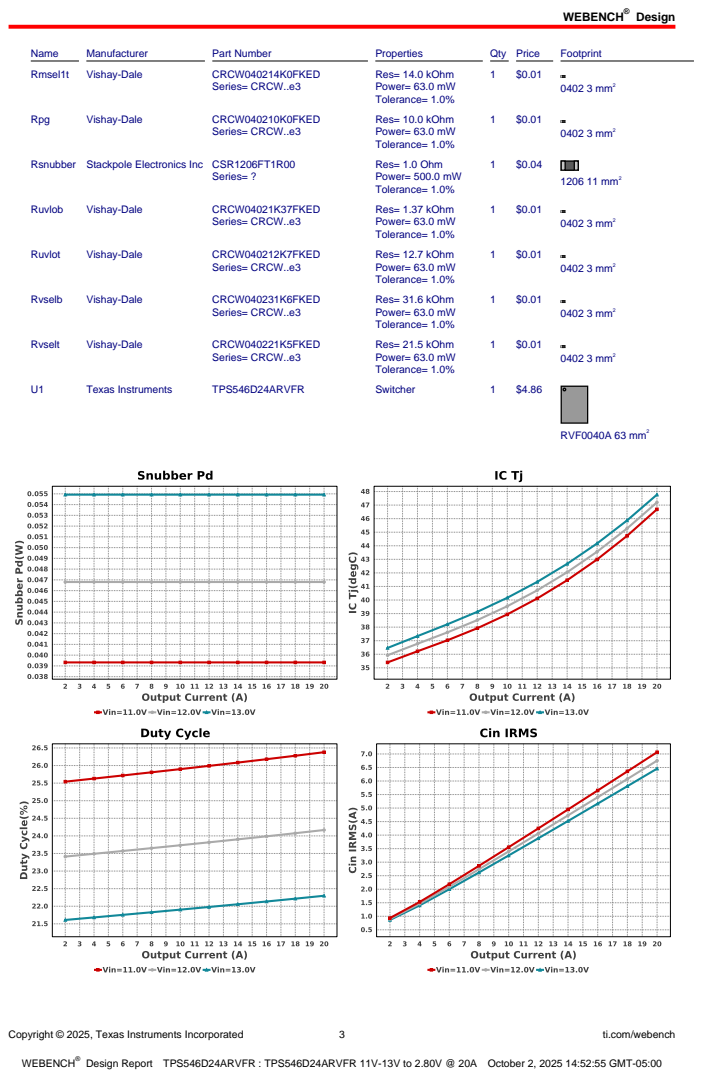
[picture p75: page 3]
Copyright © 2025, Texas Instruments Incorporated; ti.com/webench; Name; Manufacturer; Part Number; Properties; Qty Price; Footprint; Rmsel1t; Vishay-Dale; CRCW040214K0FKED; Series= CRCW..e3; Res= 14.0 kOhm Power= 63.0 mW Tolerance= 1.0%; 0402 3 mm²; Rpg; CRCW040210K0FKED; Res= 10.0 kOhm Power= 63.0 mW Tolerance= 1.0%; Series= ?; Res= 1.0 Ohm Power= 500.0 mW Tolerance= 1.0%; 1206 11 mm²; Ruvlob; CRCW04021K37FKED; Res= 1.37 kOhm Power= 63.0 mW Tolerance= 1.0%; Ruvlot; CRCW040212K7FKED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

Rsnubber Stackpole Electronics Inc CSR1206FT1R00 (http://www.seielect.com/Catalog/SEI%2Dcsr.pdf)

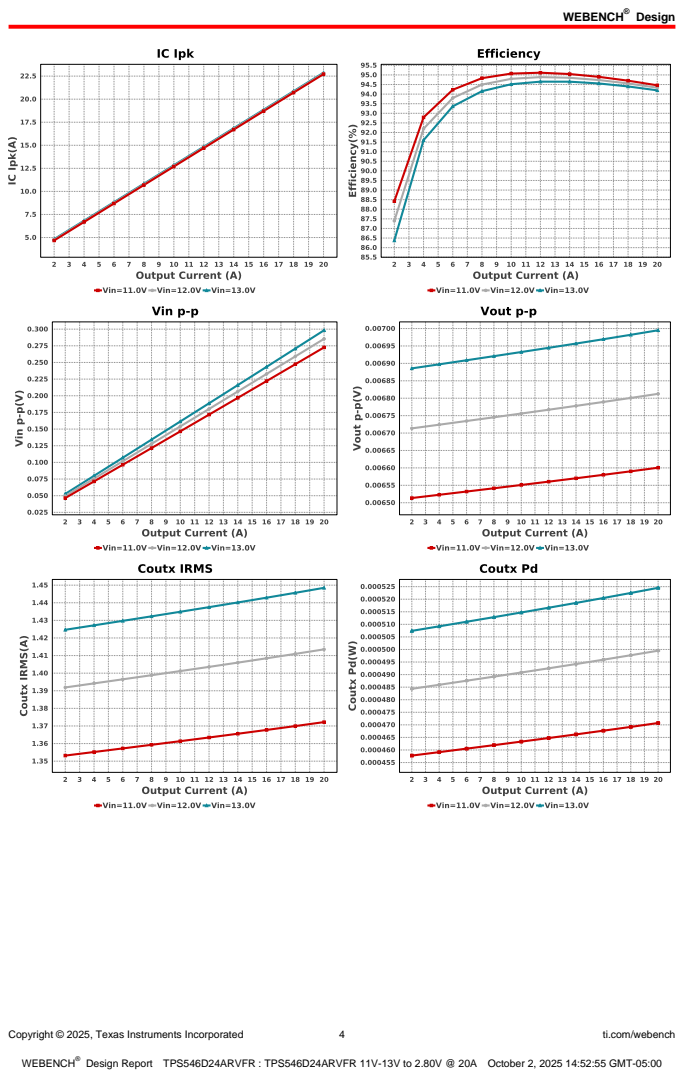
[picture p76: page 4]
Copyright © 2025, Texas Instruments Incorporated; ti.com/webench

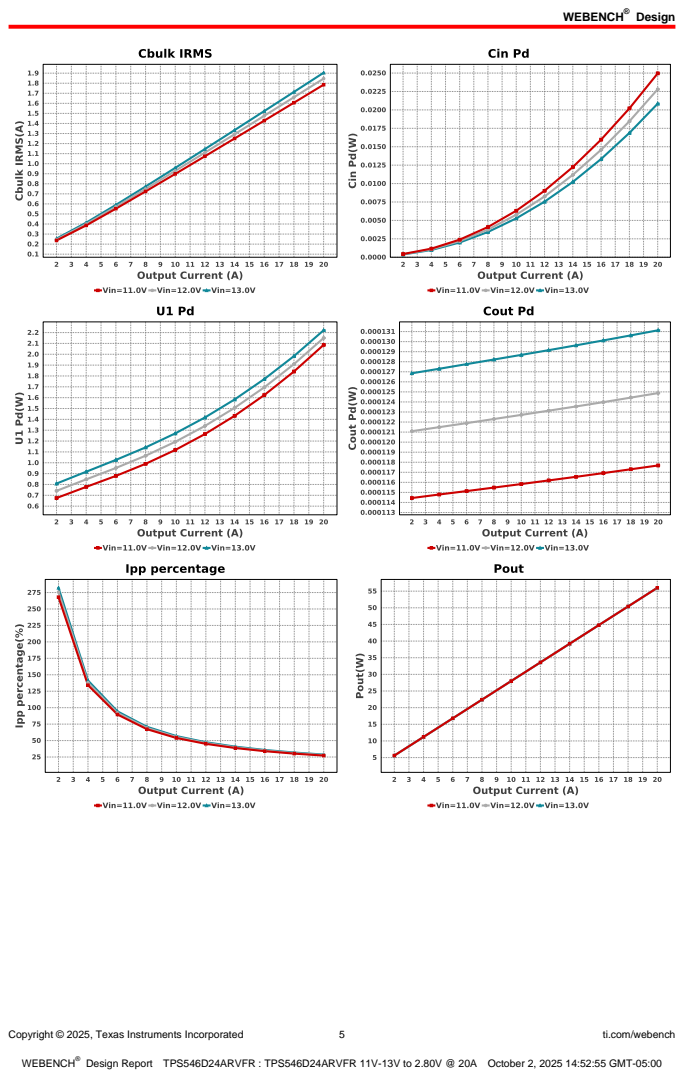
[picture p77: page 5]
Copyright © 2025, Texas Instruments Incorporated; ti.com/webench

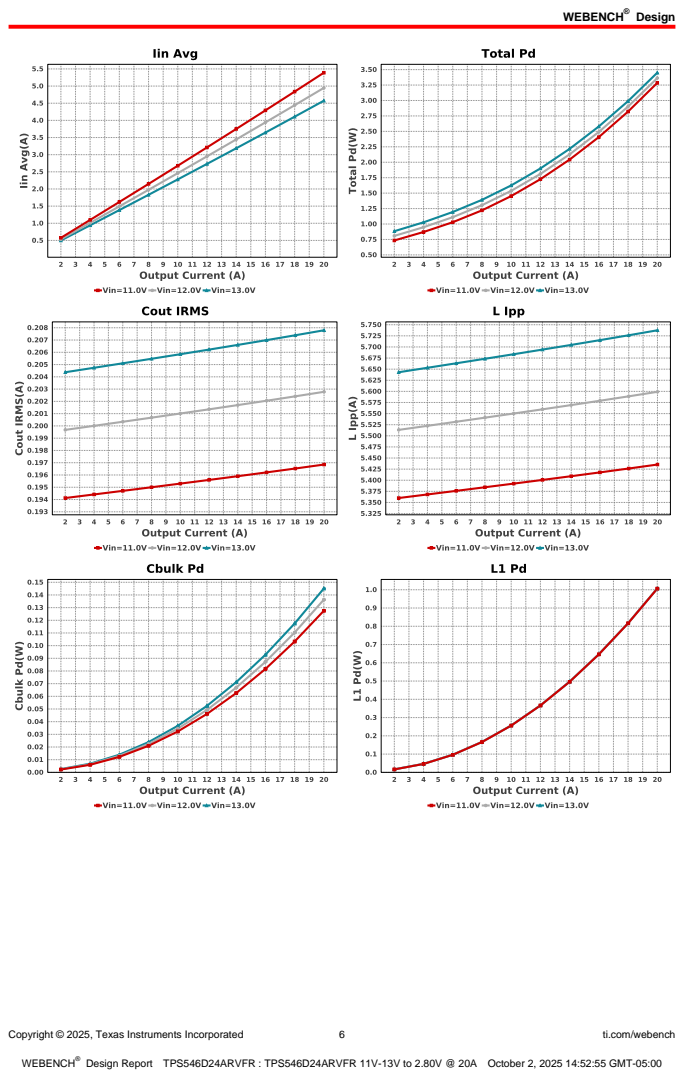
[picture p78: page 6]
Copyright © 2025, Texas Instruments Incorporated; ti.com/webench

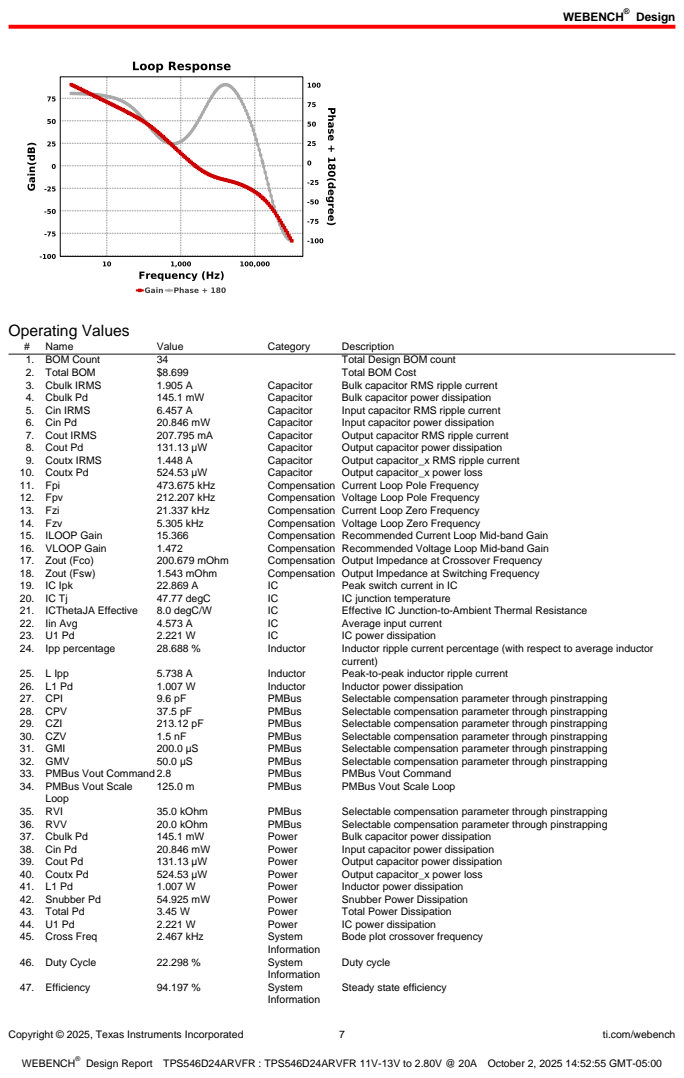
[picture p79: page 7]
Copyright © 2025, Texas Instruments Incorporated; ti.com/webench; Operating Values; Name; Value; Category; Description; 1. BOM Count; Total Design BOM count; 2. Total BOM; Total BOM Cost; 3. Cbulk IRMS; Capacitor; Bulk capacitor RMS ripple current; 4. Cbulk Pd; Bulk capacitor power dissipation; 5. Cin IRMS; Input capacitor RMS ripple current; 6. Cin Pd; Input capacitor power dissipation; 7. Cout IRMS; Output capacitor RMS ripple current; 8. Cout Pd; Output capacitor power dissipation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

34. PMBus Vout Scale
Loop

Bode plot crossover frequency

Steady state efficiency

Copyright © 2025, Texas Instruments Incorporated | 8 | ti.com/webench
# | Name | Value | Category | Description

48. FootPrint | 498.0 mm² | System
| | | Information | Total Foot Print Area of BOM components
49. Frequency | 325.0 kHz | System
| | | Information | Switching frequency
50. Gain Marg | -35.789 dB | System
| | | Information | Bode Plot Gain Margin
51. Iout | 20.0 A | System
| | | Information | Iout operating point
52. Low Freq Gain | 90.175 dB | System
| | | Information | Gain at 1Hz
53. Mode | CCM | System
| | | Information | Conduction Mode
54. Phase Marg | 48.011 deg | System
| | | Information | Bode Plot Phase Margin
55. Pout | 56.0 W | System
| | | Information | Total output power
56. Vin | 13.0 V | System
| | | Information | Vin operating point
57. Vin p-p | 298.314 mV | System
| | | Information | Peak-to-peak input voltage
58. Vout | 2.8 V | System
| | | Information | Operational Output Voltage
59. Vout Tolerance | 285.714 m% | System
| | | Information | Vout Tolerance based on IC Tolerance (no load) and voltage divider resistors if applicable
60. Vout p-p | 6.995 mV | System
| | | Information | Peak-to-peak output ripple voltage

## Design Inputs

Name | Value | Description
Iout | 20.0 | Maximum Output Current
VinMax | 13.0 | Maximum input voltage
VinMin | 11.0 | Minimum input voltage
Vout | 2.8 | Output Voltage
| base_pn | | TPS546D24A | Base Product Number
source | DC | Input Source Type
Ta | 30.0 | Ambient temperature
1. Vout Sch | 2.8 | Output voltage selected


Copyright © 2025, Texas Instruments Incorporated | 9 | ti.com/webench

## Assembly

## Component Testing

Some published data on components in datasheets such as Capacitor ESR and Inductor DC resistance is based on conservative values that will guarantee that the components always exceed the specification. For design purposes it is usually better to work with typical values. Since this data is not always available it is a good practice to measure the Capacitance and ESR values of Cin and Cout, and the inductance and DC resistance of L1 before assembly of the board. Any large discrepancies in values should be electrically simulated in WEBENCH to check for instabilities and thermally simulated in WebTHERM to make sure critical temperatures are not exceeded.

## Soldering Component to Board

If board assembly is done in house it is best to tack down one terminal of a component on the board then solder the other terminal. For surface mount parts with large tabs, such as the DPAK, the tab on the back of the package should be pre-tinned with solder, then tacked into place by one of the pins. To solder the tab town to the board place the iron down on the board while resting against the tab, heating both surfaces simultaneously. Apply light pressure to the top of the plastic case until the solder flows around the part and the part is flush with the PCB. If the solder is not flowing around the board you may need a higher wattage iron (generally 25W to 30W is enough).

## Initial Startup of Circuit

It is best to initially power up the board by setting the input supply voltage to the lowest operating input voltage 11.0V and set the input supply's current limit to zero. With the input supply off connect up the input supply to Vin and GND. Connect a digital volt meter and a load if needed to set the minimum Iout of the design from Vout and GND. Turn on the input supply and slowly turn up the current limit on the input supply.
If the voltage starts to rise on the input supply continue increasing the input supply current limit while watching the output voltage. If the current increases on the input supply, but the voltage remains near zero, then there may be a short or a component misplaced on the board. Power down the board and visually inspect for solder bridges and recheck the diode and capacitor polarities. Once the power supply circuit is operational then more extensive testing may include full load testing, transient load and line tests to compare with simulation results.

## Load Testing

The setup is the same as the initial startup, except that an additional digital voltmeter is connected between Vin and GND, a load is connected between Vout and GND and a current meter is connected in series between Vout and the load. The load must be able to handle at least rated output power + 50% ( 7.5 watts for this design). Ideally the load is supplied in the form of a variable load test unit. It can also be done in the form of suitably large power resistors. When using an oscilloscope to measure waveforms on the prototype board, the ground leads of the oscilloscope probes should be as short as possible and the area of the loop formed by the ground lead should be kept to a minimum. This will help reduce ground lead inductance and eliminate EMI noise that is not actually present in the circuit.

## Design Assistance

1. Master key : 4403CD56E2ECE12A[v1]
2. TPS546D24A Product Folder : http://www.ti.com/product/TPS546D24A : contains the data sheet and other resources.

Copyright © 2025, Texas Instruments Incorporated | 10 | ti.com/webench

Important Notice and Disclaimer

TI provides technical and reliability data (including datasheets), design resources (including reference designs), application or other design advice, web tools, safety information, and other resources AS IS and with all faults, and disclaims all warranties. These resources are intended for skilled developers designing with TI products. You are solely responsible for (1) selecting the appropriate TI products for your application, (2) designing, validating and testing your application, and (3) ensuring your application meets applicable standards, and any other safety, security, or other requirements.

These resources are subject to change without notice. TI grants you permission to use these resources only for development of an application that uses the TI products described in the resource. Other reproduction and display of these resources is prohibited. No license is granted to any other TI intellectual property right or to any third party intellectual property right. TI disclaims responsibility for, and you will fully indemnify TI and its representatives against, any claims, damages, costs, losses, and liabilities arising out of your use of these resources.

Providing these resources does not expand or otherwise alter TI's applicable Terms of Sale or other applicable terms available either on ti.com or provided in conjunction with TI products.
